Gao-Den/rk-smartwatch/rk-smartwatch-stm32f411/application/sources/app/screen/flappy_bird/base.cpp

/**
 ******************************************************************************
 * @author: GaoDen
 * @date:   10/07/2026
 ******************************************************************************
**/

#include "base.h"
#include "screen_game.h"

/* base object */
static lv_obj_t* base[BASE_NUM];

/* game image bitmap */
extern const LV_ATTRIBUTE_MEM_ALIGN LV_ATTRIBUTE_LARGE_CONST uint8_t base_map[];
lv_image_dsc_t base_img_src;

void base_bitmap_create() {
    /* base background bitmap */
    base_img_src.header.cf = LV_COLOR_FORMAT_RGB565;
    base_img_src.header.magic = LV_IMAGE_HEADER_MAGIC;
    base_img_src.header.w = 24;
    base_img_src.header.h = 60;
    base_img_src.header.stride = 24 * 2;
    base_img_src.data_size = 1440 * 2;
    base_img_src.data = base_map;
}

void base_create() {
    /* base object create */
    for (int i = 0; i < BASE_NUM; i++) {
        base[i] = lv_image_create(screen_game_playing);
        lv_image_set_src(base[i], &base_img_src);
        lv_obj_align(base[i], LV_ALIGN_BOTTOM_LEFT, i * BASE_WIDTH, 0);
    }
}

const LV_ATTRIBUTE_MEM_ALIGN LV_ATTRIBUTE_LARGE_CONST uint8_t base_map[] = {
    0xc9, 0x59, 0xc9, 0x59, 0xc9, 0x59, 0xc9, 0x59, 0xc9, 0x59, 0xc9, 0x59, 0xc9, 0x59, 0xc9, 0x59, 0xc9, 0x59, 0xc9, 0x59, 0xc9, 0x59, 0xc9, 0x59, 0xc9, 0x59, 0xc9, 0x59, 0xc9, 0x59, 0xc9, 0x59, 0xc9, 0x59, 0xc9, 0x59, 0xc9, 0x59, 0xc9, 0x59, 0xc9, 0x59, 0xc9, 0x59, 0xc9, 0x59, 0xc9, 0x59, 
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
    0xd3, 0xe6, 0xd3, 0xe6, 0xd3, 0xe6, 0xd3, 0xe6, 0xd3, 0xe6, 0xd3, 0xe6, 0xd3, 0xe6, 0xd3, 0xe6, 0xd3, 0xe6, 0xd3, 0xe6, 0xd3, 0xe6, 0xd3, 0xe6, 0xd3, 0xe6, 0xd3, 0xe6, 0xd3, 0xe6, 0xd3, 0xe6, 0xd3, 0xe6, 0xd3, 0xe6, 0xd3, 0xe6, 0xd3, 0xe6, 0xd3, 0xe6, 0xd3, 0xe6, 0xd3, 0xe6, 0xd3, 0xe6, 
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
};
