Gao-Den/rk-smartwatch/rk-smartwatch-stm32f411/application/sources/app/screen/flappy_bird/bird.cpp

/**
 ******************************************************************************
 * @author: GaoDen
 * @date:   10/07/2026
 ******************************************************************************
**/

#include "bird.h"

#include "screen_game.h"

/* bird object */
static bird_t bird;

/* bird image bitmap */
lv_image_dsc_t bird_img_src;
extern const LV_ATTRIBUTE_MEM_ALIGN LV_ATTRIBUTE_LARGE_CONST uint8_t yellow_bird_map[];

void bird_bitmap_create() {
    /* bird image bitmap */
    bird_img_src.header.cf = LV_COLOR_FORMAT_RGB565;
    bird_img_src.header.magic = LV_IMAGE_HEADER_MAGIC;
    bird_img_src.header.w = 34;
    bird_img_src.header.h = 24;
    bird_img_src.header.stride = 34 * 2;
    bird_img_src.data_size = 816 * 2;
    bird_img_src.data = yellow_bird_map;
}

void bird_create() {
    /* bird object create */
    bird.obj = lv_image_create(screen_game_playing);
    lv_image_set_src(bird.obj, &bird_img_src);

    /* bird default position */
    bird.x = 100;
    bird.y = 100;
    bird.vx = 0;
    bird.vy = BIRD_GRAVITY;
    lv_obj_align(bird.obj, LV_ALIGN_TOP_LEFT, bird.x, bird.y);
}

void bird_reset() {
    /* bird default position */
    bird.x = 100;
    bird.y = 100;
    bird.vx = 0;
    bird.vy = BIRD_GRAVITY;
    lv_obj_align(bird.obj, LV_ALIGN_TOP_LEFT, bird.x, bird.y);
}

void bird_run() {

    bird.vy += BIRD_GRAVITY;

    if (bird.y <= (215 - BIRD_HEIGHT)) {
        bird.y += bird.vy;
        lv_obj_set_y(bird.obj, (int32_t)bird.y);
    }
}

float bird_get_x() {
    return (float)bird.x;
}

float bird_get_y() {
    return (float)bird.y;
}

void bird_jump() {
    bird.vy = BIRD_JUMP_SPEED;
    bird.y += bird.vy;
    lv_obj_set_y(bird.obj, (int32_t)bird.y);
}

bool bird_game_over() {

    bird.vy += BIRD_GRAVITY;

    if (bird.y <= (215 - BIRD_HEIGHT)) {
        bird.y += bird.vy;
        lv_obj_set_y(bird.obj, (int32_t)bird.y);

        return false;
    }

    return true;
}

const LV_ATTRIBUTE_MEM_ALIGN LV_ATTRIBUTE_LARGE_CONST uint8_t yellow_bird_map[] = {
    0x19, 0x56, 0x19, 0x56, 0x19, 0x56, 0x19, 0x56, 0x19, 0x56, 0x19, 0x56, 0x19, 0x56, 0x19, 0x56, 0x19, 0x56, 0x19, 0x56, 0x19, 0x56, 0x19, 0x56, 0xc9, 0x51, 0xc9, 0x51, 0xc9, 0x51, 0xc9, 0x51, 0xc9, 0x51, 0xc9, 0x51, 0xc9, 0x51, 0xc9, 0x51, 0xc9, 0x51, 0xc9, 0x51, 0xc9, 0x51, 0xc9, 0x51, 0x19, 0x56, 0x19, 0x56, 0x19, 0x56, 0x19, 0x56, 0x19, 0x56, 0x19, 0x56, 0x19, 0x56, 0x19, 0x56, 0x19, 0x56, 0x19, 0x56, 
    0x19, 0x56, 0x19, 0x56, 0x19, 0x56, 0x19, 0x56, 0x19, 0x56, 0x19, 0x56, 0x19, 0x56, 0x19, 0x56, 0x19, 0x56, 0x19, 0x56, 0x19, 0x56, 0x19, 0x56, 0xc9, 0x51, 0xc9, 0x51, 0xc9, 0x51, 0xc9, 0x51, 0xc9, 0x51, 0xc9, 0x51, 0xc9, 0x51, 0xc9, 0x51, 0xc9, 0x51, 0xc9, 0x51, 0xc9, 0x51, 0xc9, 0x51, 0x19, 0x56, 0x19, 0x56, 0x19, 0x56, 0x19, 0x56, 0x19, 0x56, 0x19, 0x56, 0x19, 0x56, 0x19, 0x56, 0x19, 0x56, 0x19, 0x56, 
    0x19, 0x56, 0x19, 0x56, 0x19, 0x56, 0x19, 0x56, 0x19, 0x56, 0x19, 0x56, 0x19, 0x56, 0x19, 0x56, 0xc9, 0x51, 0xc9, 0x51, 0xc9, 0x51, 0xc9, 0x51, 0xd2, 0xfe, 0xd2, 0xfe, 0xd2, 0xfe, 0xd2, 0xfe, 0xd2, 0xfe, 0xd2, 0xfe, 0xc9, 0x51, 0xc9, 0x51, 0xff, 0xff, 0xff, 0xff, 0xff, 0xff, 0xff, 0xff, 0xc9, 0x51, 0xc9, 0x51, 0x19, 0x56, 0x19, 0x56, 0x19, 0x56, 0x19, 0x56, 0x19, 0x56, 0x19, 0x56, 0x19, 0x56, 0x19, 0x56, 
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
};
