Gao-Den/rk-smartwatch/rk-smartwatch-stm32f411/application/sources/app/screen/flappy_bird/pipe.cpp

/**
 ******************************************************************************
 * @author: GaoDen
 * @date:   10/07/2026
 ******************************************************************************
**/

#include "pipe.h"
#include "screen_game.h"

/* pipe object */
static pipe_t pipes[PIPE_NUM];

/* pipe image bitmap */
lv_image_dsc_t pipe_img_src;
extern const LV_ATTRIBUTE_MEM_ALIGN LV_ATTRIBUTE_LARGE_CONST uint8_t pipe_green_map[];

void pipe_bitmap_create() {
    /* pipe image bitmap */
    pipe_img_src.header.cf = LV_COLOR_FORMAT_RGB565;
    pipe_img_src.header.magic = LV_IMAGE_HEADER_MAGIC;
    pipe_img_src.header.w = 40;
    pipe_img_src.header.h = 100;
    pipe_img_src.header.stride = 40 * 2;
    pipe_img_src.data_size = 4000 * 2;
    pipe_img_src.data = pipe_green_map;
}

void pipe_create() {
    /* pipe image create */
    for (uint8_t i = 0; i < PIPE_NUM; i++) {
        pipes[i].x = 50 + i * PIPE_DISTANCE_X;
        pipes[i].vx = PIPE_DEFAULT_SPEED;
        pipes[i].gap_y = 50 + (rand() % 51);
        pipes[i].bird_passed = false;

        pipes[i].top = lv_image_create(screen_game_playing);
        lv_image_set_src(pipes[i].top, &pipe_img_src);
        lv_image_set_rotation(pipes[i].top, 1800);
        lv_obj_set_pos(pipes[i].top, (int32_t)pipes[i].x, (pipes[i].gap_y - PIPE_HEIGHT));

        pipes[i].bottom = lv_image_create(screen_game_playing);
        lv_image_set_src(pipes[i].bottom, &pipe_img_src);
        lv_obj_set_pos(pipes[i].bottom, (int32_t)pipes[i].x, (pipes[i].gap_y + PIPE_DISTANCE_Y));
    }
}

void pipe_run() {
    int16_t max_x = 0;

    for (uint8_t i = 0; i < PIPE_NUM; i++) {
        if (pipes[i].x > max_x) {
            max_x = pipes[i].x;
        }
    }

    for (uint8_t i = 0; i < PIPE_NUM; i++) {

        pipes[i].x += pipes[i].vx;

        if (pipes[i].x < -PIPE_WIDTH) {
            pipes[i].x = max_x + PIPE_DISTANCE_X;
            pipes[i].bird_passed = false;
            max_x = pipes[i].x;
            pipes[i].gap_y = 50 + (rand() % 51);
        }

        lv_obj_set_pos(pipes[i].top, (int32_t)pipes[i].x, (pipes[i].gap_y - PIPE_HEIGHT));
        lv_obj_set_pos(pipes[i].bottom, (int32_t)pipes[i].x, (pipes[i].gap_y + PIPE_DISTANCE_Y));
    }
}

pipe_t* pipe_get(uint8_t index) {
    if (index >= PIPE_NUM) {
        return NULL;
    }
    return &pipes[index];
}

const LV_ATTRIBUTE_MEM_ALIGN LV_ATTRIBUTE_LARGE_CONST uint8_t pipe_green_map[] = {
    0xc9, 0x59, 0xc9, 0x59, 0xc9, 0x59, 0xc9, 0x59, 0xc9, 0x59, 0xc9, 0x59, 0xc9, 0x59, 0xc9, 0x59, 0xc9, 0x59, 0xc9, 0x59, 0xc9, 0x59, 0xc9, 0x59, 0xc9, 0x59, 0xc9, 0x59, 0xc9, 0x59, 0xc9, 0x59, 0xc9, 0x59, 0xc9, 0x59, 0xc9, 0x59, 0xc9, 0x59, 0xc9, 0x59, 0xc9, 0x59, 0xc9, 0x59, 0xc9, 0x59, 0xc9, 0x59, 0xc9, 0x59, 0xc9, 0x59, 0xc9, 0x59, 0xc9, 0x59, 0xc9, 0x59, 0xc9, 0x59, 0xc9, 0x59, 0xc9, 0x59, 0xc9, 0x59, 0xc9, 0x59, 0xc9, 0x59, 0xc9, 0x59, 0xc9, 0x59, 0xc9, 0x59, 0xc9, 0x59, 
    0xc9, 0x59, 0x0a, 0x73, 0x0b, 0x84, 0x2c, 0x8c, 0x2c, 0x8c, 0x4c, 0x8c, 0x6c, 0x94, 0x6c, 0x94, 0x6c, 0x94, 0x8d, 0x94, 0x8d, 0x94, 0x6c, 0x94, 0x6c, 0x94, 0x6c, 0x94, 0x4c, 0x8c, 0x4c, 0x94, 0x6c, 0x94, 0x4c, 0x8c, 0x2c, 0x8c, 0x2c, 0x8c, 0x0b, 0x84, 0x0b, 0x84, 0xeb, 0x83, 0xca, 0x7b, 0xca, 0x7b, 0xaa, 0x7b, 0x8a, 0x73, 0x89, 0x73, 0x69, 0x73, 0x69, 0x6b, 0x49, 0x6b, 0x28, 0x6b, 0x28, 0x63, 0x08, 0x63, 0x08, 0x63, 0xe7, 0x5a, 0xe7, 0x5a, 0xc7, 0x5a, 0x48, 0x5a, 0xc9, 0x59, 
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
};
