Gao-Den/rk-smartwatch/esp32-s3-weather-station/main/app/task_console.h

/**
 ******************************************************************************
 * @author: GaoDen
 * @date:   25/03/2025
 ******************************************************************************
**/

#ifndef __TASK_CONSOLE_H__
#define __TASK_CONSOLE_H__

extern void task_console_handler(void* argv);

#endif /* __TASK_CONSOLE_H__ */
