Gao-Den/rk-smartwatch/esp32-s3-weather-station/main/app/task_life.h

/**
 ******************************************************************************
 * @author: GaoDen
 * @date:   25/03/2025
 ******************************************************************************
**/

#ifndef __TASK_LIFE_H__
#define __TASK_LIFE_H__

extern void task_life_handler(void* argv);

#endif /* __TASK_LIFE_H__ */
