Gao-Den/rk-smartwatch/esp32-s3-weather-station/main/app/task_polling.h

/**
 ******************************************************************************
 * @author: GaoDen
 * @date:   16/12/2025
 ******************************************************************************
**/

#ifndef __TASK_POLLING_H__
#define __TASK_POLLING_H__

#define HARDWARE_POLLING_PERIOD         (1000) /* 1000ms */

extern void task_polling_handler(void* argv);

#endif /* __TASK_POLLING_H__ */
