Gao-Den/rk-smartwatch/rk-link/sources/sys/startup/sys_startup.h

/**
 ******************************************************************************
 * @author: GaoDen
 * @date:   18/11/2024
 ******************************************************************************
**/

#ifndef __SYS_STARTUP_H__
#define __SYS_STARTUP_H__

#ifdef __cplusplus
extern "C" {
#endif 

#include <stdint.h>
#include <stdio.h>

#ifdef __cplusplus
}
#endif

#endif /* __SYS_STARTUP_H__ */
