Gao-Den/rk-smartwatch/rk-smartwatch-stm32f411/application/sources/app/task_console.h

/**
 ******************************************************************************
 * @author: GaoDen
 * @date:   02/02/2026
 ******************************************************************************
**/

#ifndef __TASK_CONSOLE_H__
#define __TASK_CONSOLE_H__

#ifdef __cplusplus
extern "C" {
#endif

#include <stdio.h>
#include <stdint.h>
#include <string.h>
#include <stdbool.h>

#include "ring_buffer.h"

#define SHELL_RING_BUFFER_REV_MAX_SIZE      (256)
#define SHELL_CMD_INPUT_MAX_SIZE            (32)

typedef struct {
    uint8_t index;
    uint8_t data[SHELL_CMD_INPUT_MAX_SIZE];
} shell_t;

extern uint8_t buffer_console_rev[SHELL_RING_BUFFER_REV_MAX_SIZE];
extern ring_buffer_char_t ring_buffer_console_rev;

extern void sys_console_getc(volatile uint8_t c);
extern void task_console();

#ifdef __cplusplus
}
#endif

#endif /* __TASK_CONSOLE_H__ */
